Sienna-Zhang/512_final/Documentation/circuit diagram.kicad_sch

## KiCad design Documentation/circuit diagram.kicad_sch (2025-12-03)

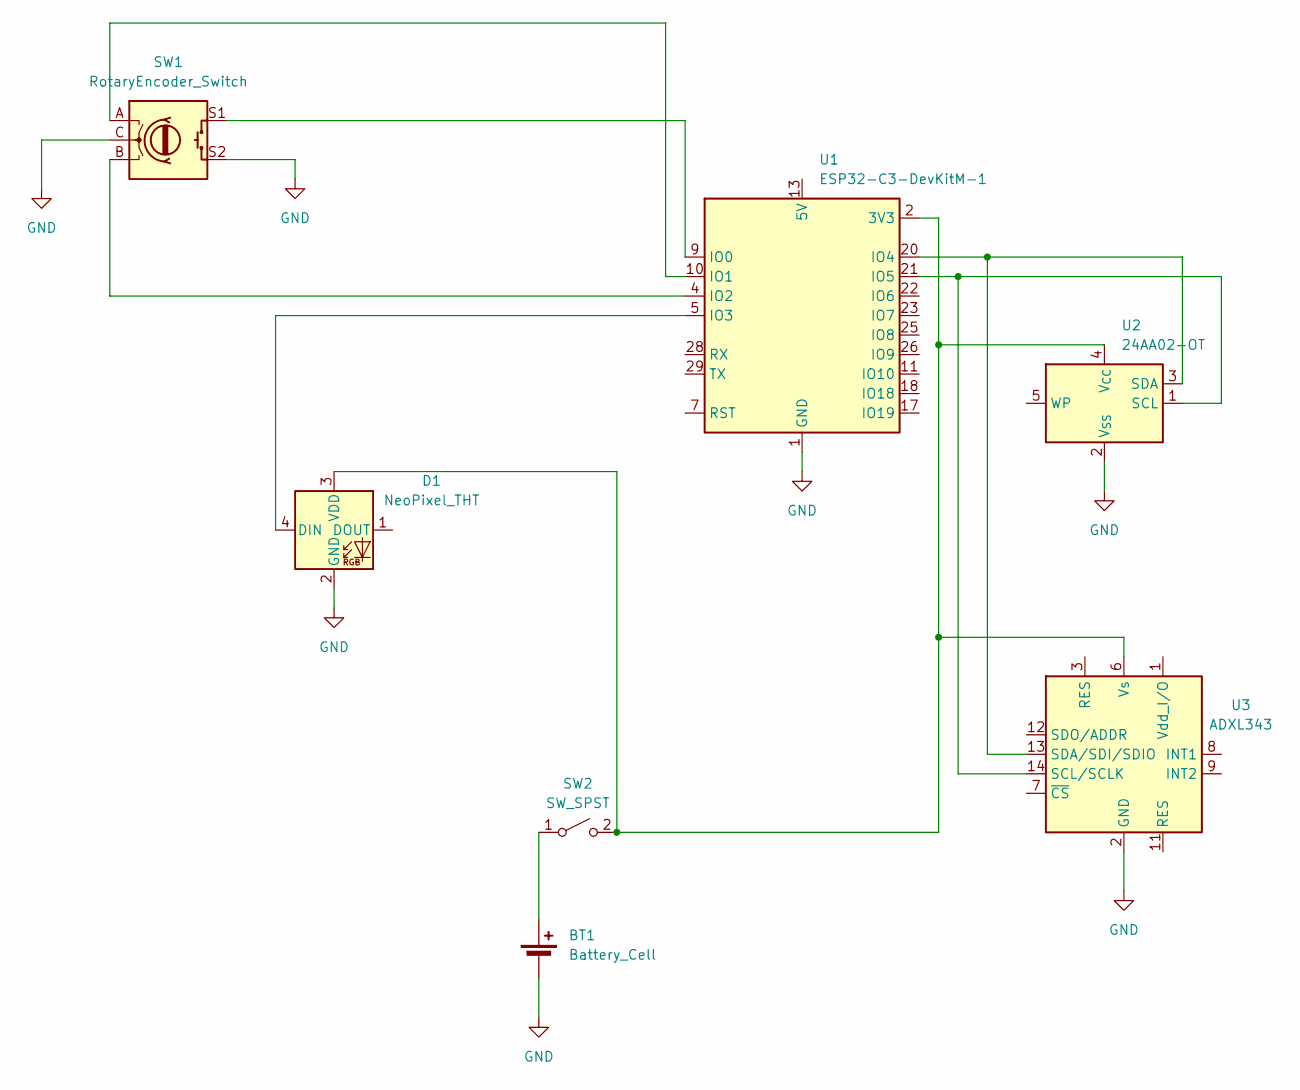
[picture p3: schematic circuit diagram.kicad_sch]

Parts:
BT1: Battery_Cell
D1: NeoPixel_THT
SW1: RotaryEncoder_Switch
SW2: SW_SPST
U1: ESP32-C3-DevKitM-1
U2: 24AA02-OT; OLED-128O064D
U3: ADXL343; LGA-14_3x5mm_P0.8mm_LayoutBorder1x6y

Connections:
GND: BT1.2 (-), D1.2 (GND), SW1.C, SW1.S2, U1.1 (GND), U1.6 (GND), U1.8 (GND), U1.12 (GND), U1.15 (GND), U1.16 (GND), U1.19 (GND), U1.24 (GND), U1.27 (GND), U1.30 (GND), U2.2 (V_{SS}), U3.2 (GND), U3.4 (GND), U3.5 (GND)
unnamed: BT1.1 (+), SW2.1 (A)
unnamed: D1.3 (VDD), SW2.2 (B), U1.2 (3V3), U1.3 (3V3), U2.4 (V_{CC}), U3.6 (Vs)
unnamed: D1.4 (DIN), U1.5 (IO3)
unnamed: SW1.A, U1.10 (IO1)
unnamed: SW1.B, U1.4 (IO2)
unnamed: SW1.S1, U1.9 (IO0)
unnamed: U1.13 (5V), U1.14 (5V)
unnamed: U1.20 (IO4), U2.3 (SDA), U3.13 (SDA/SDI/SDIO)
unnamed: U1.21 (IO5), U2.1 (SCL), U3.14 (SCL/SCLK)
